der/marvin/motor-base/pico-controller/uproximity.py

# Attempt to drive HC-SR04 Ultrasonic proximity sensor
# Adapted from https://microcontrollerslab.com/hc-sr04-ultrasonic-sensor-raspberry-pi-pico-micropython-tutorial/

import machine
from machine import Pin
import time

class Proximity:
    """
    Driver to use the untrasonic sensor HC-SR04.
    The sensor range is between 2cm and 4m.
    The timeouts received listening to echo pin return -1
    """
    # echo_timeout_us is based in chip range limit (400cm)
    def __init__(self, trigger_pin=21, echo_pin=22, echo_timeout_us=500*2*30):
        """
        trigger_pin: Output pin to send pulses
        echo_pin: Readonly pin to measure the distance. The pin should be protected with 1k resistor
        echo_timeout_us: Timeout in microseconds to listen to echo pin. 
        By default is based in sensor limit range (4m)
        """
        self.echo_timeout_us = echo_timeout_us
        self.trigger = Pin(trigger_pin, mode=Pin.OUT, pull=None)
        self.trigger.value(0)
        self.echo = Pin(echo_pin, mode=Pin.IN, pull=None)

    def _send_pulse_and_wait(self):
        """
        Send the pulse to trigger and listen on echo pin.
        """
        self.trigger.value(0) # Stabilize the sensor
        time.sleep_us(5)
        self.trigger.value(1)
        time.sleep_us(10)
        self.trigger.value(0)
        try:
            pulse_time = machine.time_pulse_us(self.echo, 1, self.echo_timeout_us)
            if pulse_time < 0:
                return -1
            return pulse_time
        except OSError as ex:
            if ex.args[0] == 110: # 110 = ETIMEDOUT
                return -1
            raise ex

    def distance_mm(self):
        """
        Get the distance in milimeters without floating point operations.
        """
        pulse_time = self._send_pulse_and_wait()

        # To calculate the distance we get the pulse_time and divide it by 2 
        # (out and back) and by 2.91 (time for sound to travel 1mm) = 5.82
        mm = pulse_time * 100 // 582
        return mm

    def distance_cm(self):
        """
        Get the distance in centimeter (as float)
        """
        pulse_time = self._send_pulse_and_wait()

        cms = pulse_time / 58.2
        return cms
