der/marvin/pico-controller/merged_test.py

# Initialise hardware and framebuf before importing modules.
from color_setup import ssd,sd,touch  # Create a display instance
from gui.core.nanogui import refresh
refresh(ssd, True)  # Initialise and clear display.

# Now import other modules
from gui.widgets.label import Label
from gui.widgets.dial import Dial, Pointer
import cmath
import utime
from gui.core.writer import CWriter

# Font for CWriter
import gui.fonts.freesans20 as font
from gui.core.colors import *

def load_image(file: str):
    refresh(ssd)  # Initialise display.
    with open(file, "rb") as f:
        f.readinto(ssd.mvb)
    refresh(ssd)  # Display the image

def aclock():
    uv = lambda phi : cmath.rect(1, phi)  # Return a unit vector of phase phi
    pi = cmath.pi
    days = ('Monday', 'Tuesday', 'Wednesday', 'Thursday', 'Friday', 'Saturday',
            'Sunday')
    months = ('Jan', 'Feb', 'March', 'April', 'May', 'June', 'July',
              'Aug', 'Sept', 'Oct', 'Nov', 'Dec')
    # Instantiate CWriter
    CWriter.set_textpos(ssd, 0, 0)  # In case previous tests have altered it
    wri = CWriter(ssd, font, GREEN, BLACK, verbose=False)
    wri.set_clip(True, True, False)

    # Instantiate displayable objects
    dial = Dial(wri, 2, 2, height = 150, ticks = 12, bdcolor=None, label=240, pip=False)  # Border in fg color
    lbltim = Label(wri, 200, 2, 35)
    hrs = Pointer(dial)
    mins = Pointer(dial)
    secs = Pointer(dial)

    # Temporary check of coords
    Label(wri, 0, 160, 'Hello world!')

    hstart =  0 + 0.7j  # Pointer lengths and position at top
    mstart = 0 + 0.92j
    sstart = 0 + 0.92j 
    while True:
        t = utime.localtime()
        hrs.value(hstart * uv(-t[3]*pi/6 - t[4]*pi/360), YELLOW)
        mins.value(mstart * uv(-t[4] * pi/30), YELLOW)
        secs.value(sstart * uv(-t[5] * pi/30), RED)
        lbltim.value('{:02d}.{:02d}.{:02d}'.format(t[3], t[4], t[5]))
        dial.text('{} {} {} {}'.format(days[t[6]], t[2], months[t[1] - 1], t[0]))
        refresh(ssd)
        print('Touch: ', touch.touch_get())
        utime.sleep(1)

def main():
    if sd:
        load_image('/sd/cat-small.bin')
    else:
        load_image('flower.bin')
    aclock()

main()
